ryomuk/TangNanoDCJ11MEM/applications/baremetal/TangNanoDCJ11MEM_project.20240707/impl/gwsynthesis/TangNanoDCJ11MEM_project_syn_resource.html

# Hierarchy Module Resource

MODULE NAME | REG NUMBER | ALU NUMBER | LUT NUMBER | DSP NUMBER | BSRAM NUMBER | SSRAM NUMBER | ROM16 NUMBER
top (C:/wks/ework/FPGA/TangNano/20k/TangNanoDCJ11MEM/TangNanoDCJ11MEM_project_baremetal/src/top.v) | 113 | 71 | 101 | - | 32 | - | -
|--uart_rx_inst (C:/wks/ework/FPGA/TangNano/20k/TangNanoDCJ11MEM/TangNanoDCJ11MEM_project_baremetal/src/top.v) | 40 | 15 | 39 | - | - | - | -
|--uart_tx_inst (C:/wks/ework/FPGA/TangNano/20k/TangNanoDCJ11MEM/TangNanoDCJ11MEM_project_baremetal/src/top.v) | 32 | - | 54 | - | - | - | -
|--onboard_rgb_led (C:/wks/ework/FPGA/TangNano/20k/TangNanoDCJ11MEM/TangNanoDCJ11MEM_project_baremetal/src/top.v) | 45 | - | 81 | - | - | - | -
