ryomuk/TangNanoDCJ11MEM/applications/tapebasic/TangNanoDCJ11MEM_project/impl/gwsynthesis/TangNanoDCJ11MEM_project_syn_resource.html

# Hierarchy Module Resource

MODULE NAME | REG NUMBER | ALU NUMBER | LUT NUMBER | DSP NUMBER | BSRAM NUMBER | SSRAM NUMBER | ROM16 NUMBER
top (C:/wks/ework/FPGA/TangNano/20k/tmp/TangNanoDCJ11MEM/applications/tapebasic/TangNanoDCJ11MEM_project/src/top.v) | 122 | 71 | 136 | - | 32 | - | -
|--onboard_rgb_led (C:/wks/ework/FPGA/TangNano/20k/tmp/TangNanoDCJ11MEM/applications/tapebasic/TangNanoDCJ11MEM_project/src/top.v) | 45 | - | 84 | - | - | - | -
|--uart_rx_inst (C:/wks/ework/FPGA/TangNano/20k/tmp/TangNanoDCJ11MEM/applications/tapebasic/TangNanoDCJ11MEM_project/src/top.v) | 40 | 15 | 33 | - | - | - | -
|--uart_tx_inst (C:/wks/ework/FPGA/TangNano/20k/tmp/TangNanoDCJ11MEM/applications/tapebasic/TangNanoDCJ11MEM_project/src/top.v) | 33 | 15 | 34 | - | - | - | -
|--sdtape_inst (C:/wks/ework/FPGA/TangNano/20k/tmp/TangNanoDCJ11MEM/applications/tapebasic/TangNanoDCJ11MEM_project/src/top.v) | 323 | 71 | 439 | - | 2 | 2 | -
